gowenrw/DFW_InfoSec_Badge_2018/prototype-images/20180618_191832.jpg

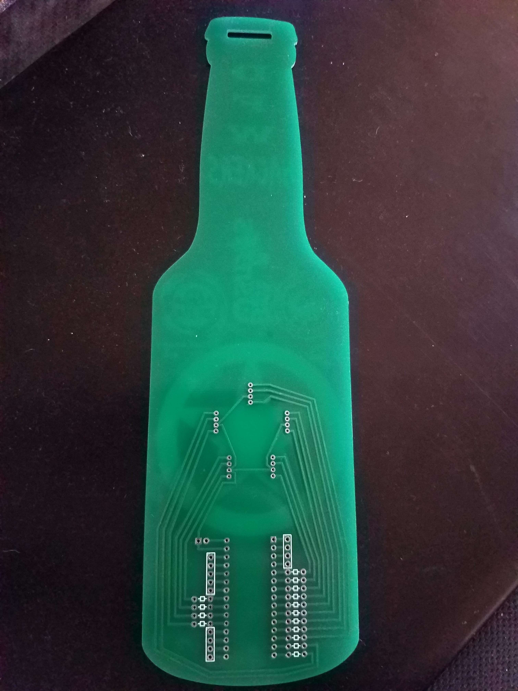
prototype-images/20180618_191832.jpg
