gowenrw/DFW_InfoSec_Badge_2018/prototype-images/20180618_192003.jpg

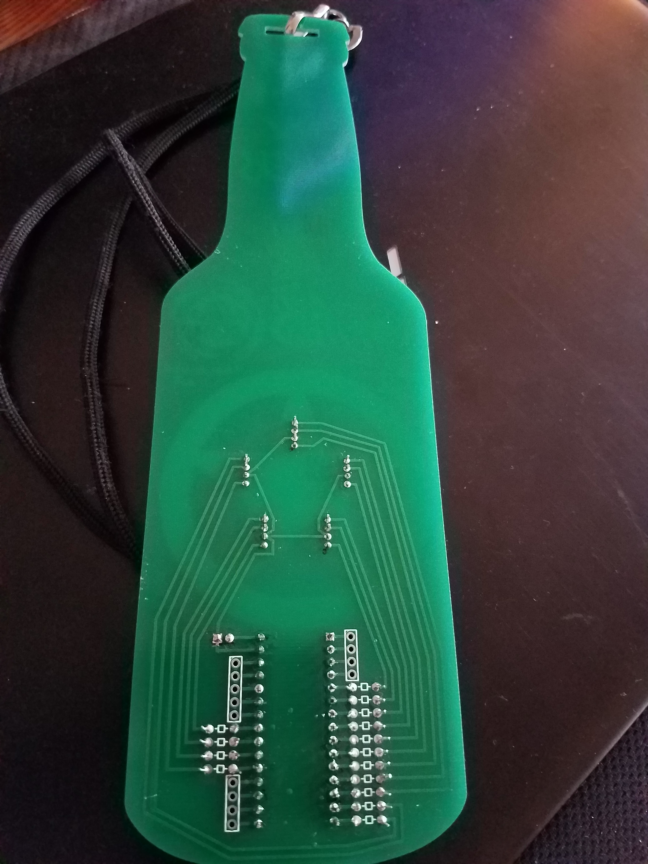
prototype-images/20180618_192003.jpg
