gowenrw/DFW_InfoSec_Badge_2018/prototype-images/20180618_192643.gif

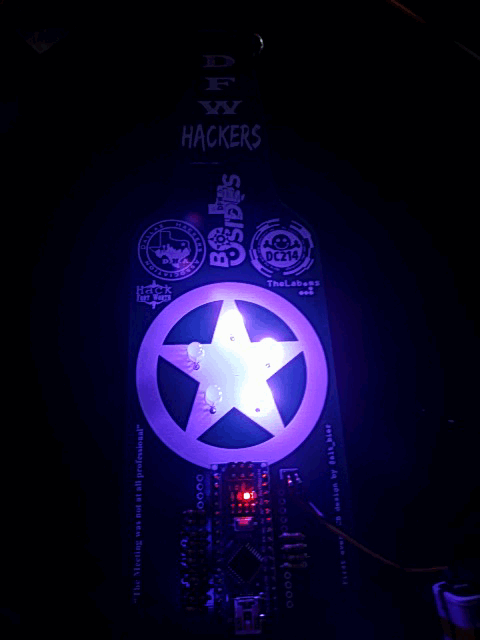
prototype-images/20180618_192643.gif
