gowenrw/DFW_InfoSec_Badge_2018/components/arduino/NanoPinOut.png

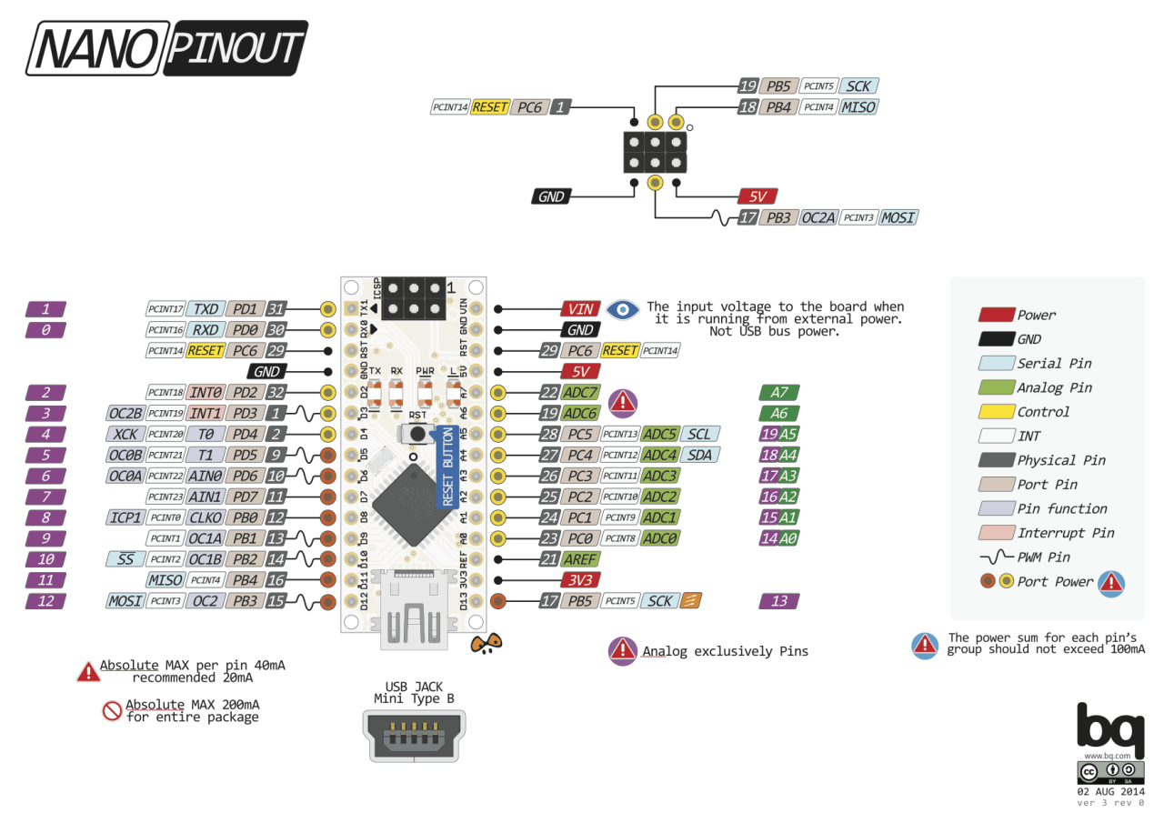
components/arduino/NanoPinOut.png
