gowenrw/DFW_InfoSec_Badge_2018/components/other/Battery_Connector-C70374_C70375_9V-Ia.png

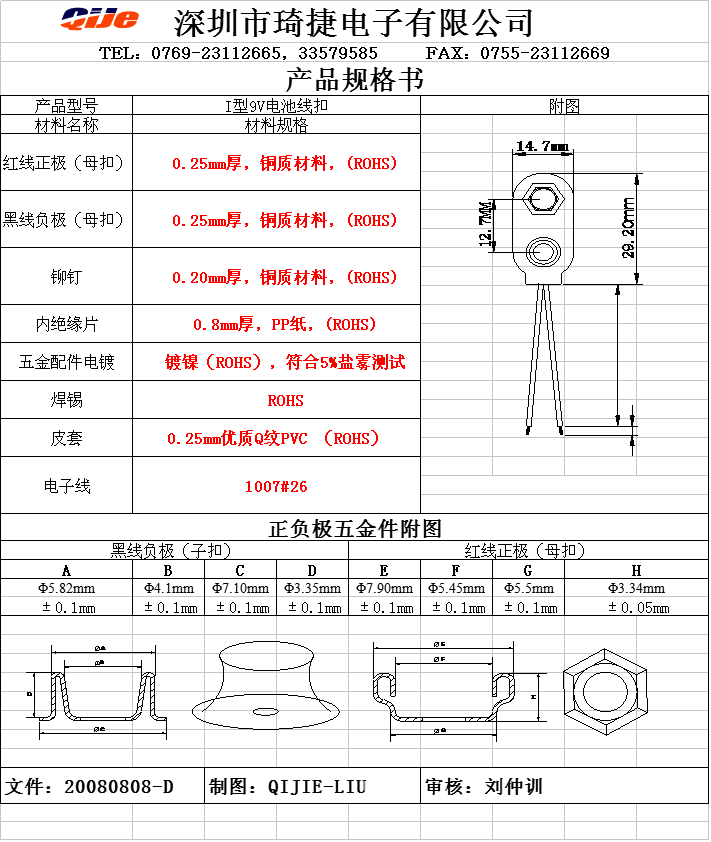
components/other/Battery_Connector-C70374_C70375_9V-Ia.png
